SeaBoiii/FYP/.images/3D_PCB_2.png

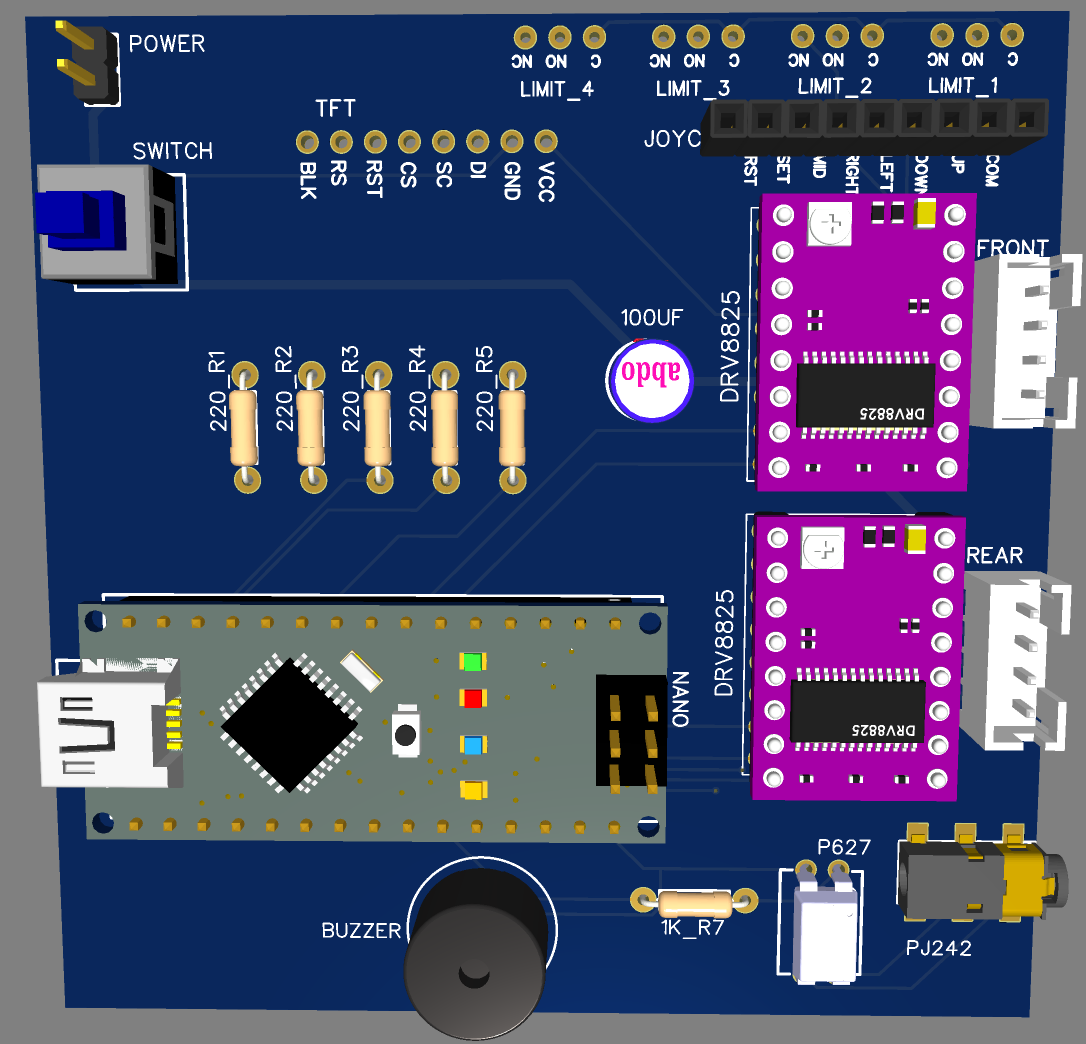
.images/3D_PCB_2.png
