SeaBoiii/FYP/.images/272100559_10159610648204771_5538881790551053657_n.jpg

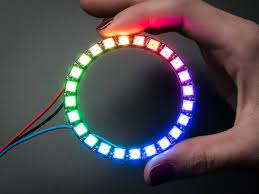
.images/272100559_10159610648204771_5538881790551053657_n.jpg
