SeaBoiii/FYP/.images/20220317182252_002.jpg

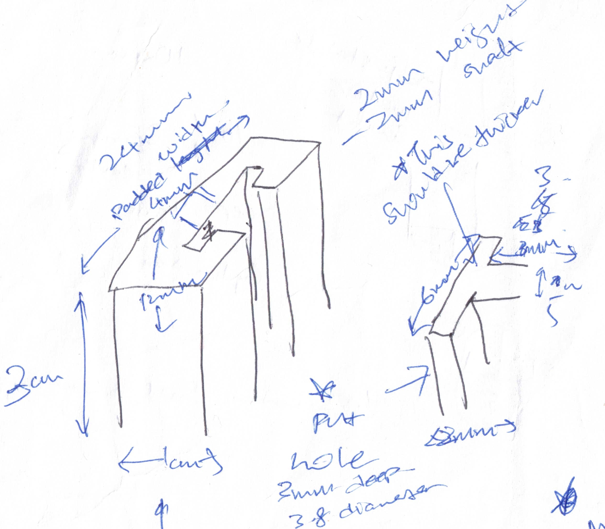
.images/20220317182252_002.jpg
