SeaBoiii/FYP/.images/_DSC9705-2 copy Small.jpg

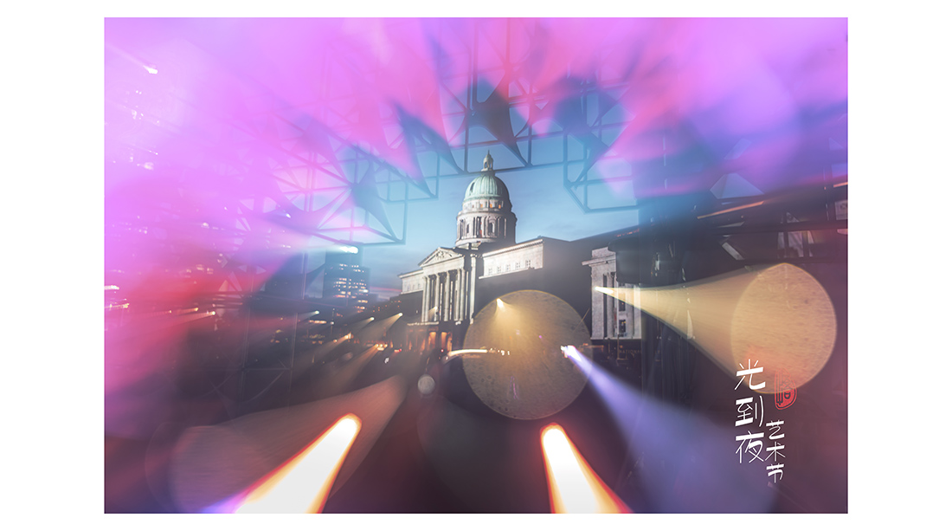
.images/_DSC9705-2 copy Small.jpg
