SeaBoiii/FYP/.images/Create a pattern Flowchart.png

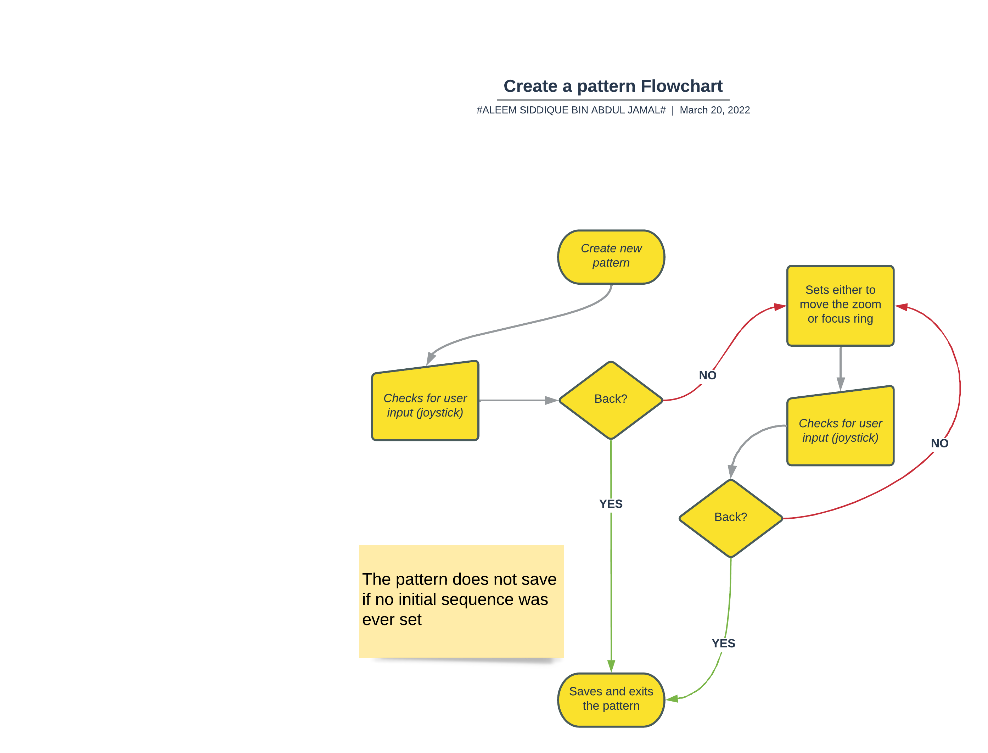
.images/Create a pattern Flowchart.png
