SeaBoiii/FYP/.images/gears.png

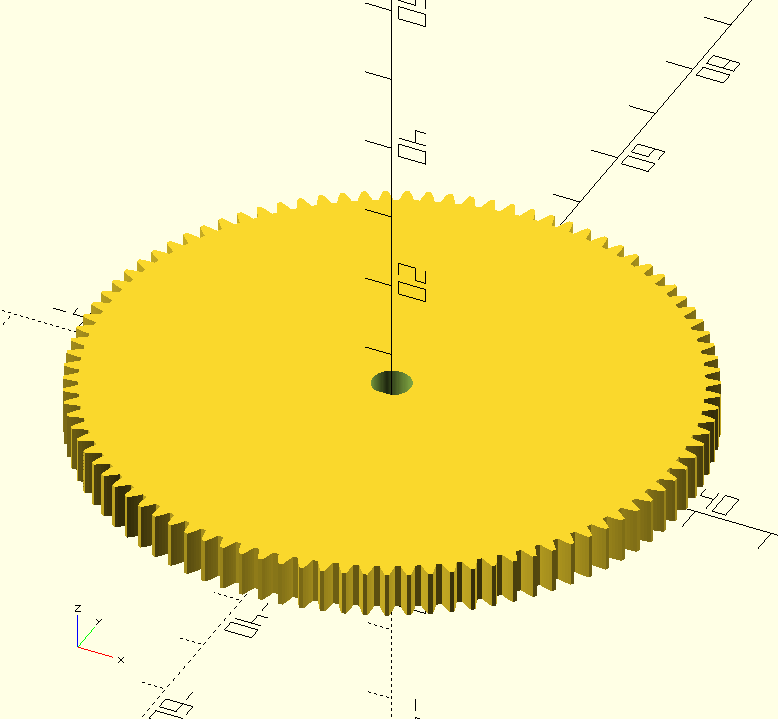
.images/gears.png
