SeaBoiii/FYP/.images/Main Loop Flowchart (1).png

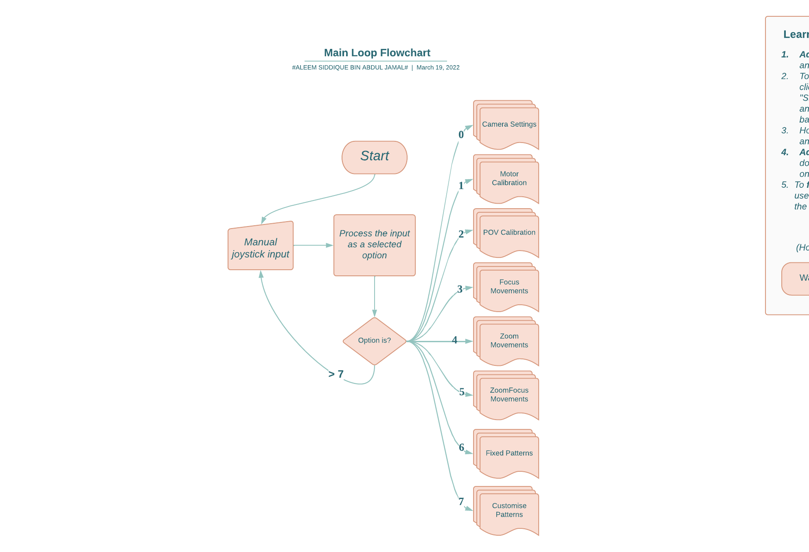
.images/Main Loop Flowchart (1).png
