SeaBoiii/FYP/.images/Merged Layer.png

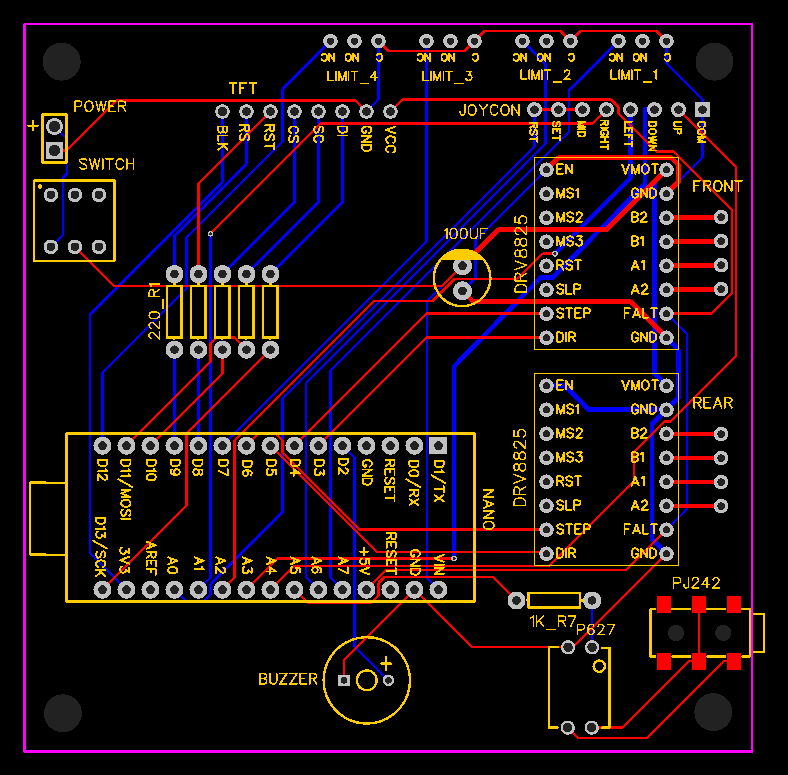
.images/Merged Layer.png
