SeaBoiii/FYP/.images/PCB_Board.png

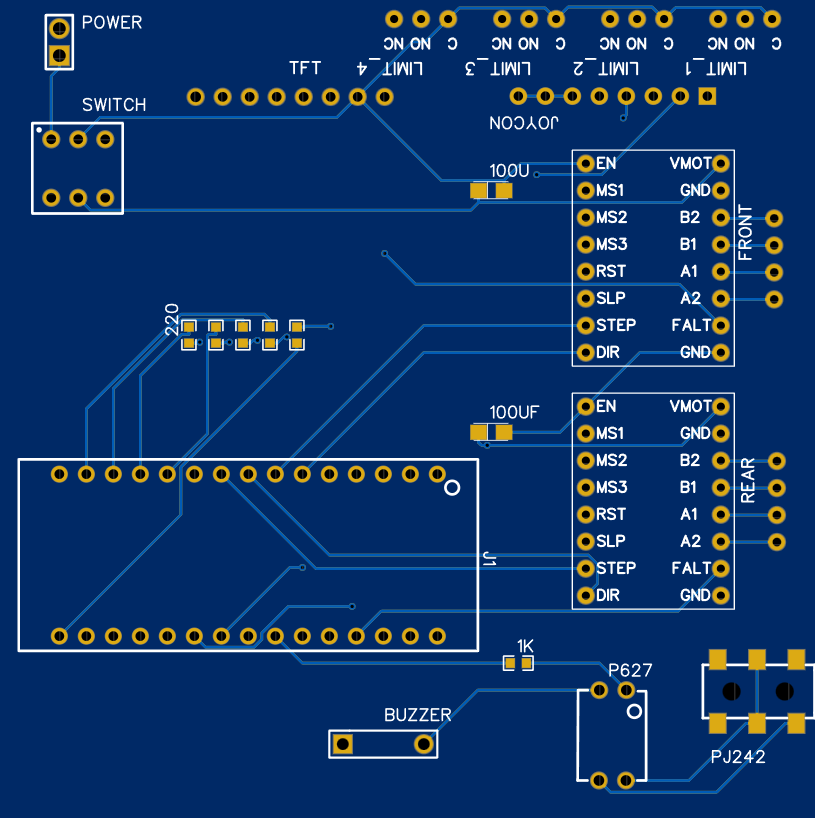
.images/PCB_Board.png
