SeaBoiii/FYP/.images/top_layer_PCB.png

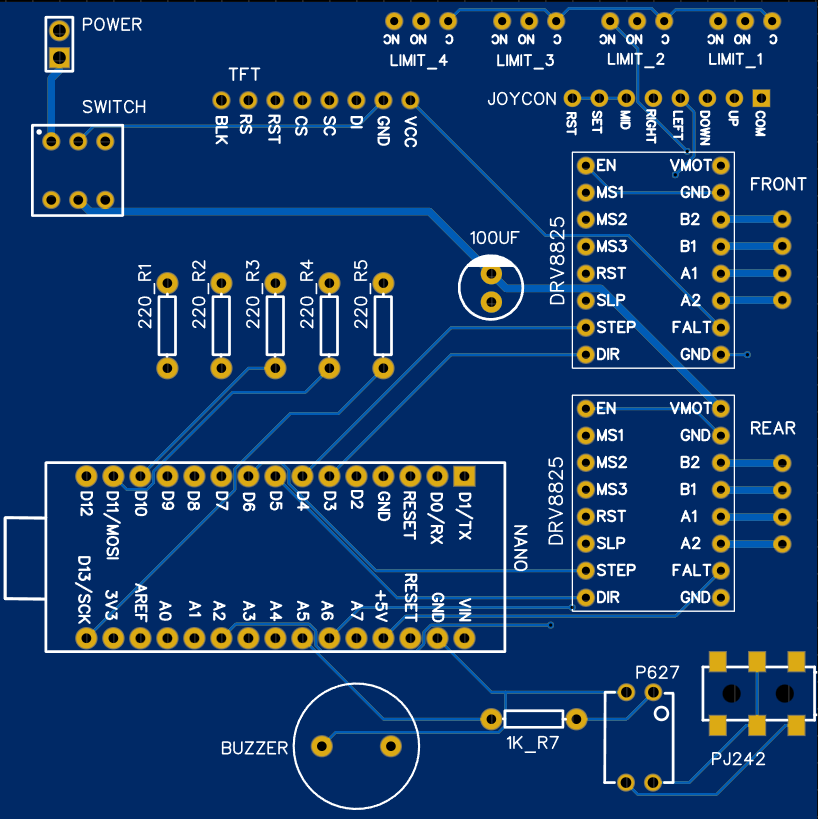
.images/top_layer_PCB.png
